JavierGONL/bd-pi/imagenes/BDPi reducido.jpg

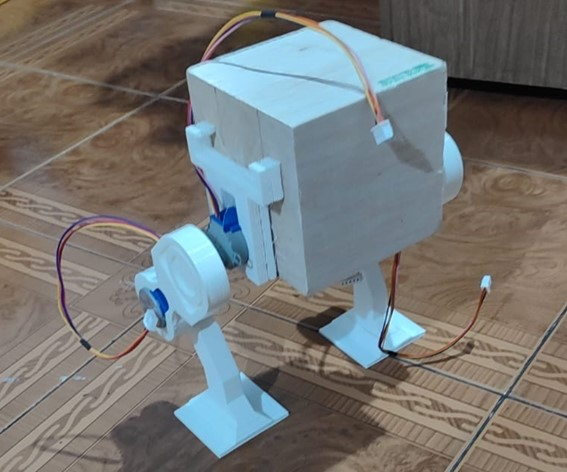
imagenes/BDPi reducido.jpg
