JavierGONL/bd-pi/imagenes/Black Box Actualizada.jpg

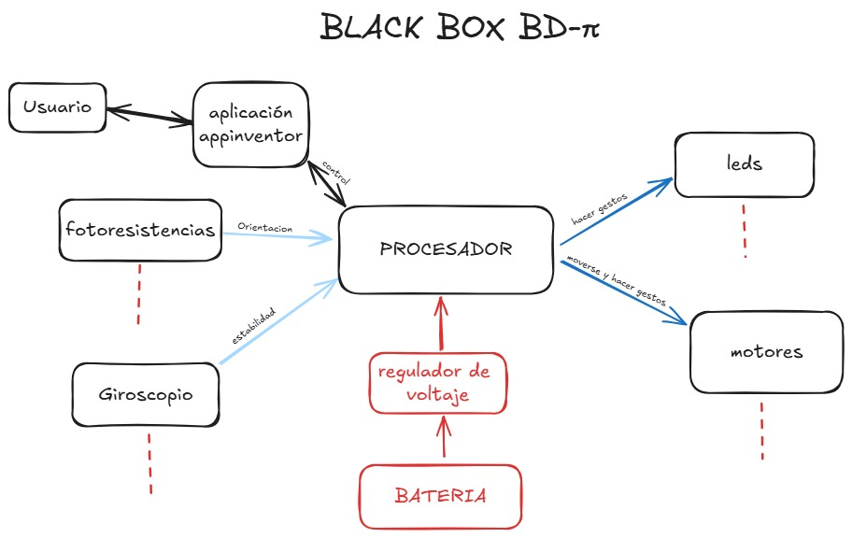
imagenes/Black Box Actualizada.jpg
