JavierGONL/bd-pi/imagenes/Caja Pico.jpg

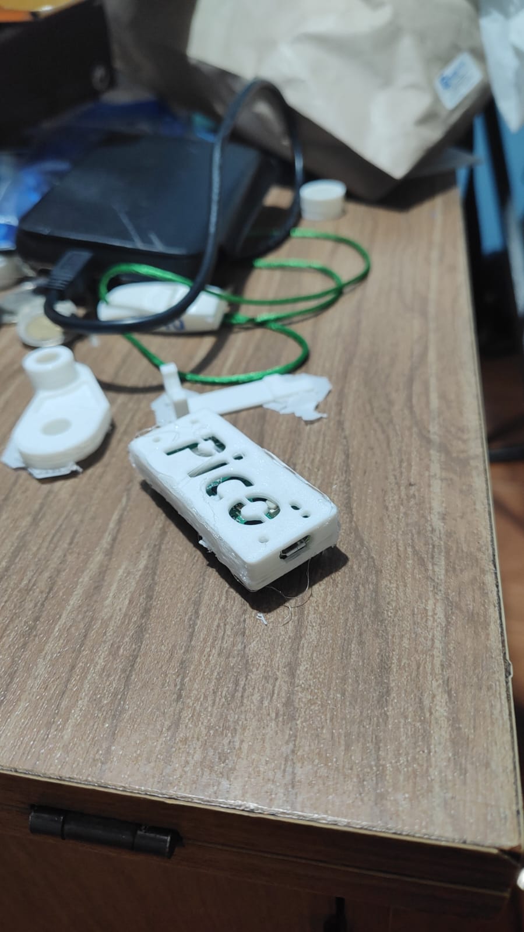
imagenes/Caja Pico.jpg
