JavierGONL/bd-pi/imagenes/Codigo App inventor.jpg

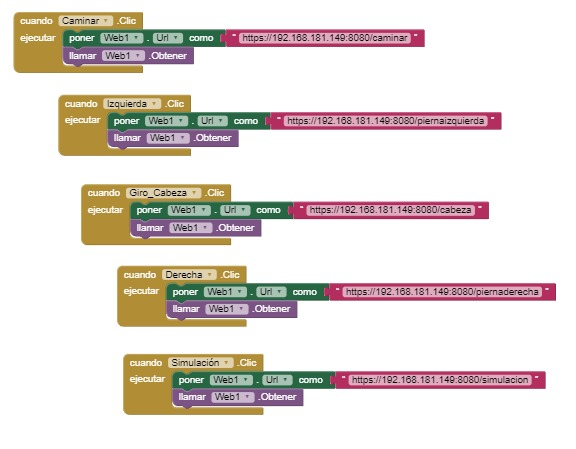
imagenes/Codigo App inventor.jpg
