JavierGONL/bd-pi/imagenes/esquematico.png

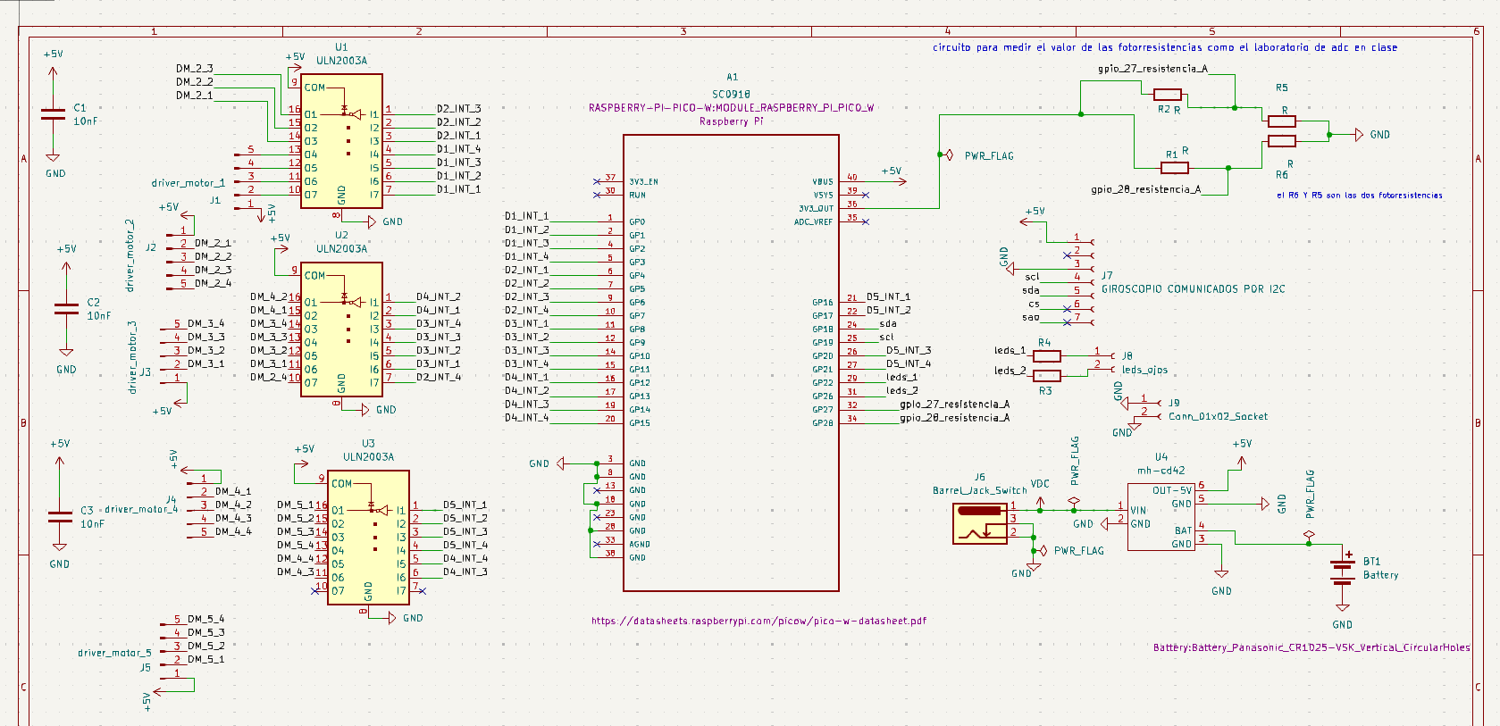
imagenes/esquematico.png
