JavierGONL/bd-pi/imagenes/Gray Box Actualizada.jpg

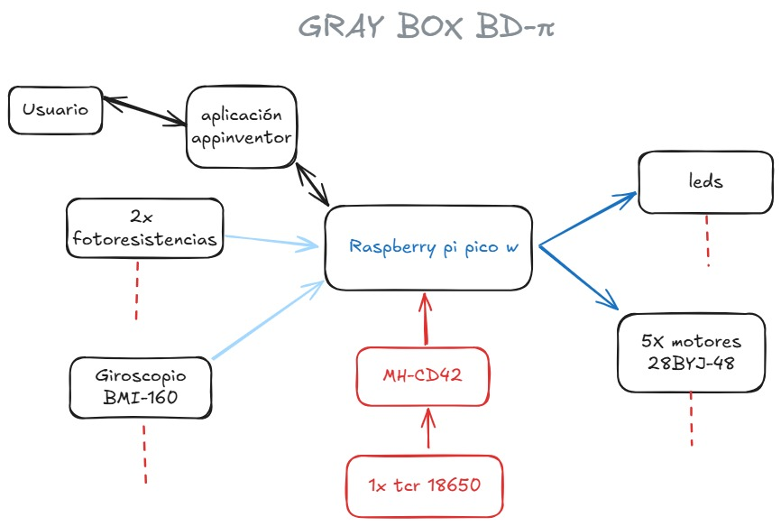
imagenes/Gray Box Actualizada.jpg
