JavierGONL/bd-pi/imagenes/Idea de Piernas.png

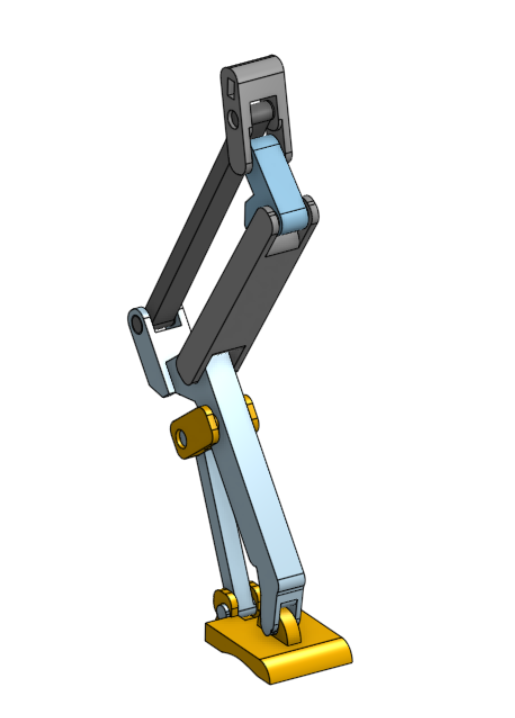
imagenes/Idea de Piernas.png
