JavierGONL/bd-pi/imagenes/Idea Final Pata Motores.jpg

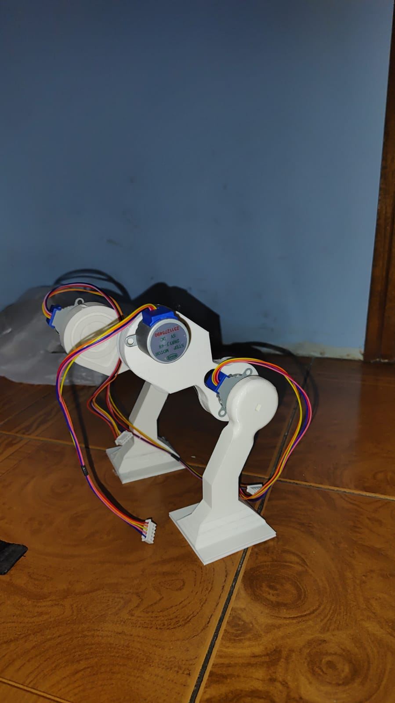
imagenes/Idea Final Pata Motores.jpg
