JavierGONL/bd-pi/imagenes/Imagen de Carga.jpg

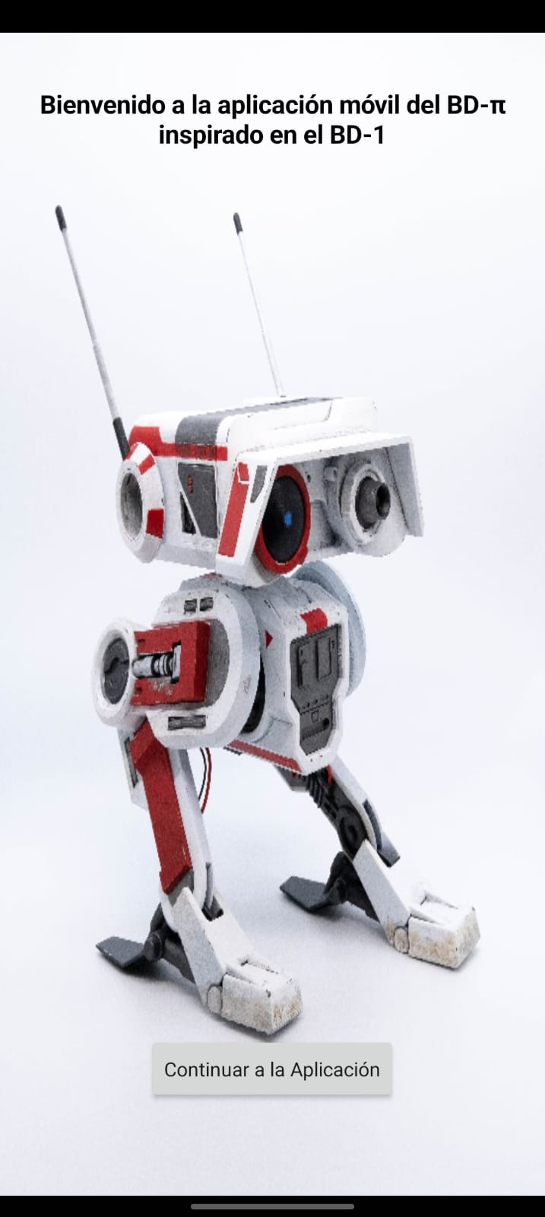
imagenes/Imagen de Carga.jpg
