JavierGONL/bd-pi/imagenes/Imagen Funcionalididad.jpg

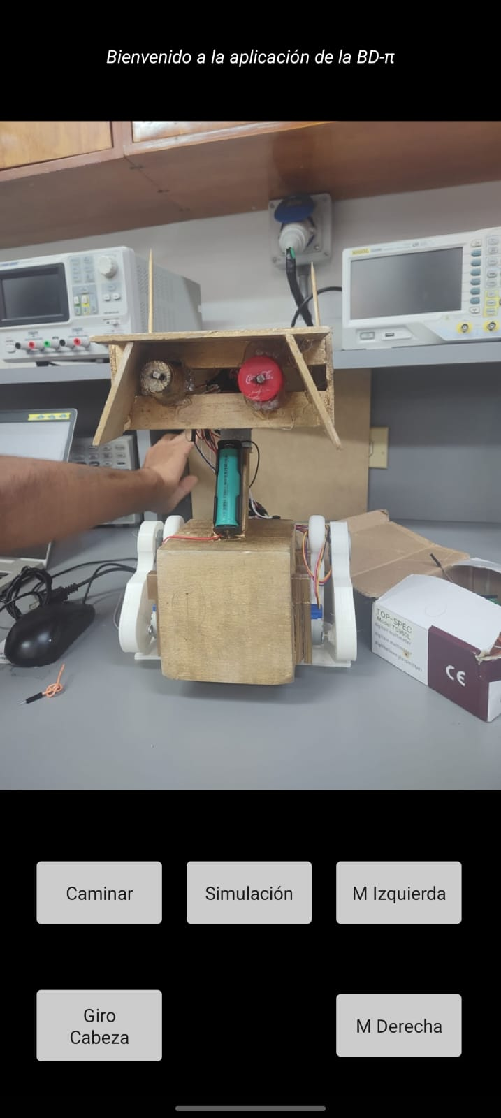
imagenes/Imagen Funcionalididad.jpg
