JavierGONL/bd-pi/imagenes/Imagen PCB.jpg

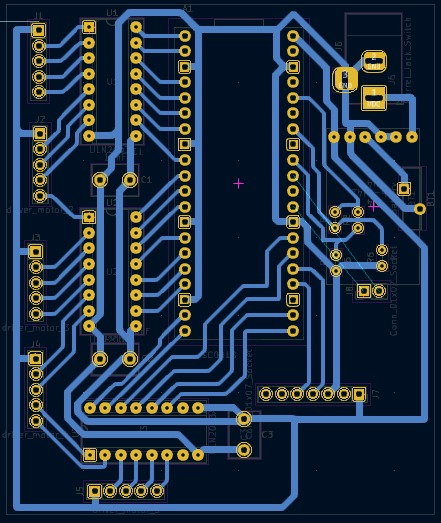
imagenes/Imagen PCB.jpg
