JavierGONL/bd-pi/imagenes/IMG_20240908_172200059.jpg

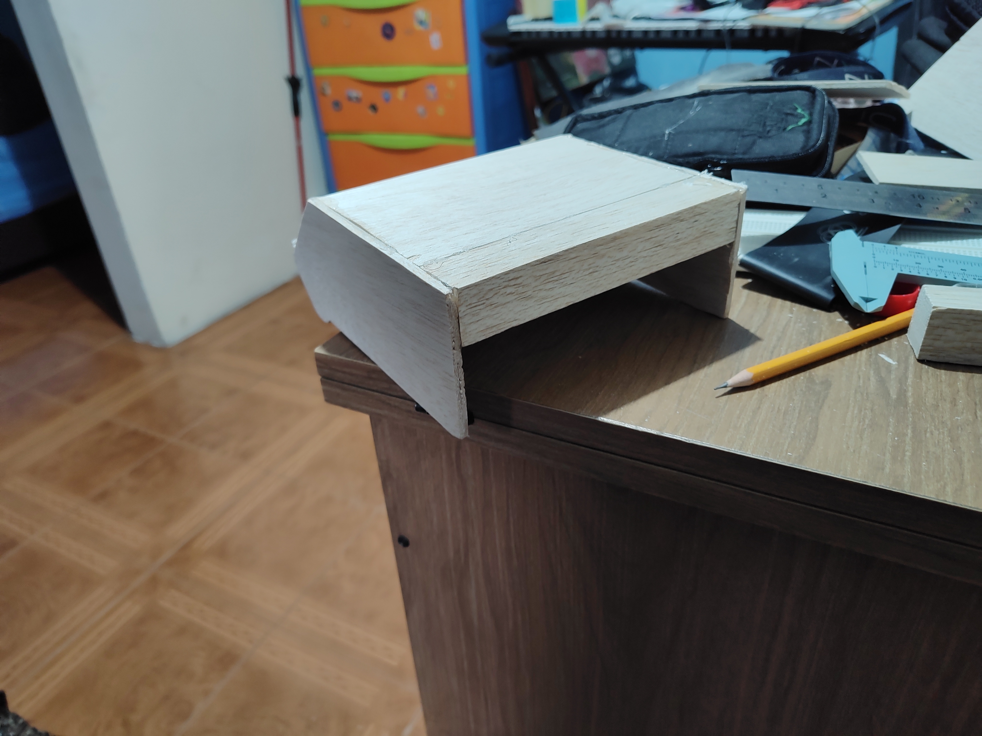
imagenes/IMG_20240908_172200059.jpg
