JavierGONL/bd-pi/imagenes/IMG_20240909_112415441.jpg

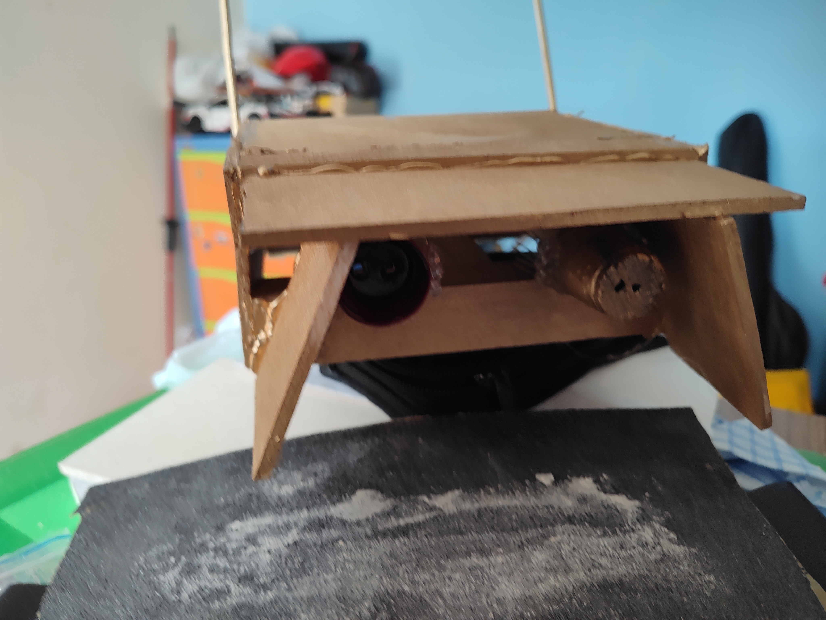
imagenes/IMG_20240909_112415441.jpg
