JavierGONL/bd-pi/imagenes/IMG_20240916_122246359.jpg

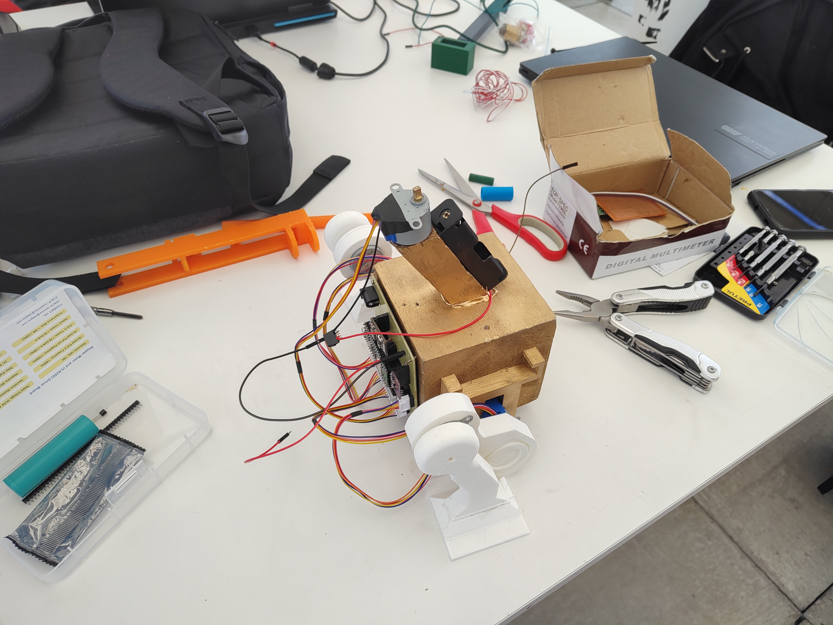
imagenes/IMG_20240916_122246359.jpg
