JavierGONL/bd-pi/imagenes/IMG_20240919_124108.jpg

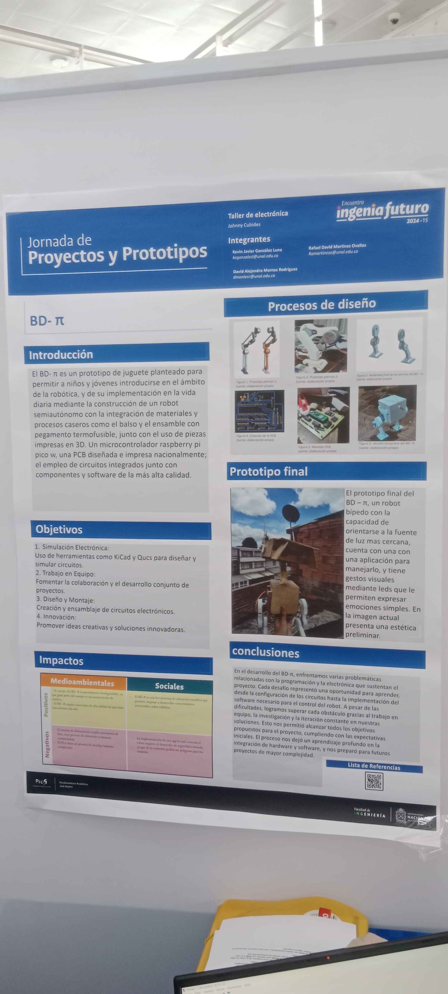
imagenes/IMG_20240919_124108.jpg
