JavierGONL/bd-pi/imagenes/IMG_20240919_124112.jpg

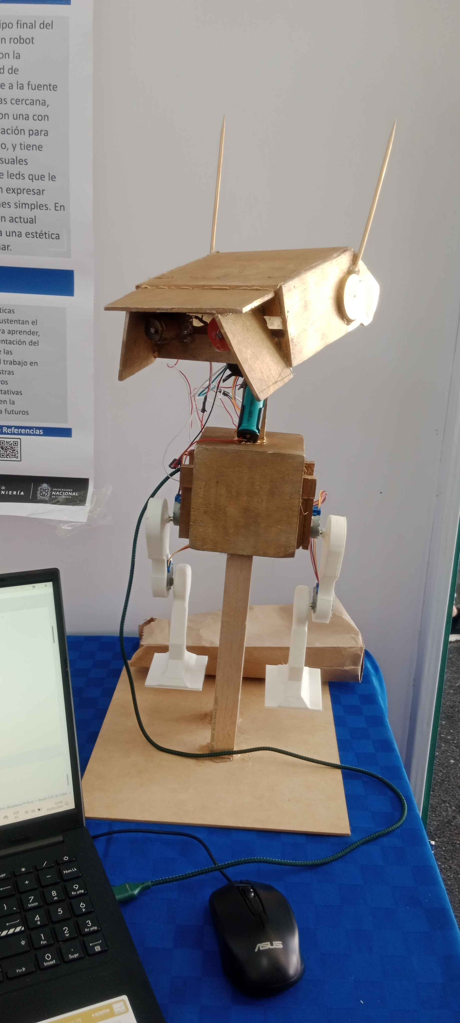
imagenes/IMG_20240919_124112.jpg
