JavierGONL/bd-pi/imagenes/IMG_20240919_124115.jpg

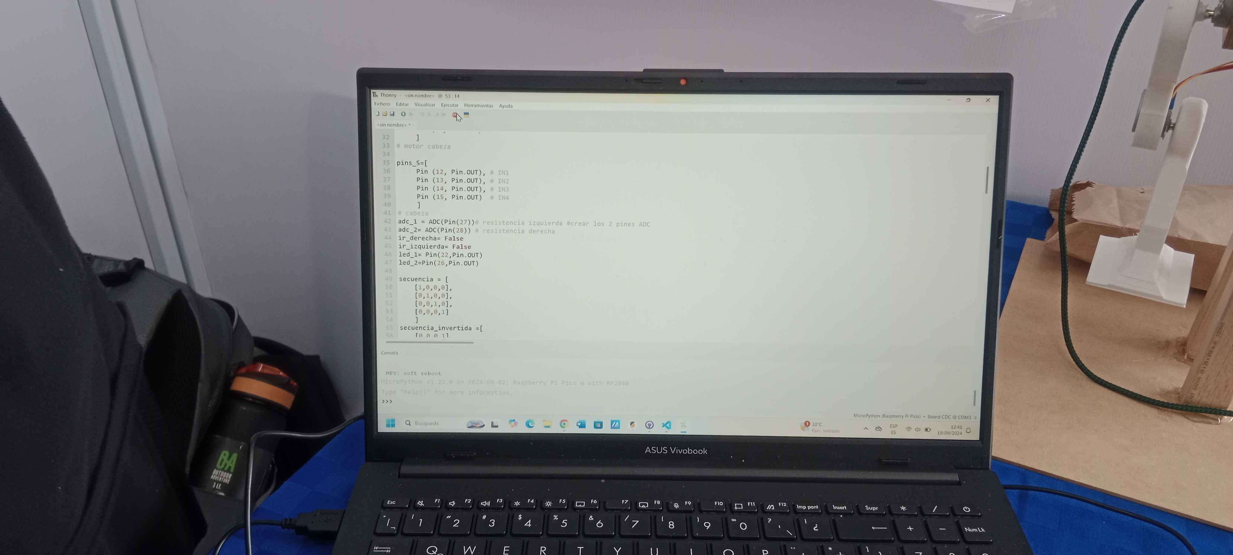
imagenes/IMG_20240919_124115.jpg
