JavierGONL/bd-pi/imagenes/IMG_20240919_124416.jpg

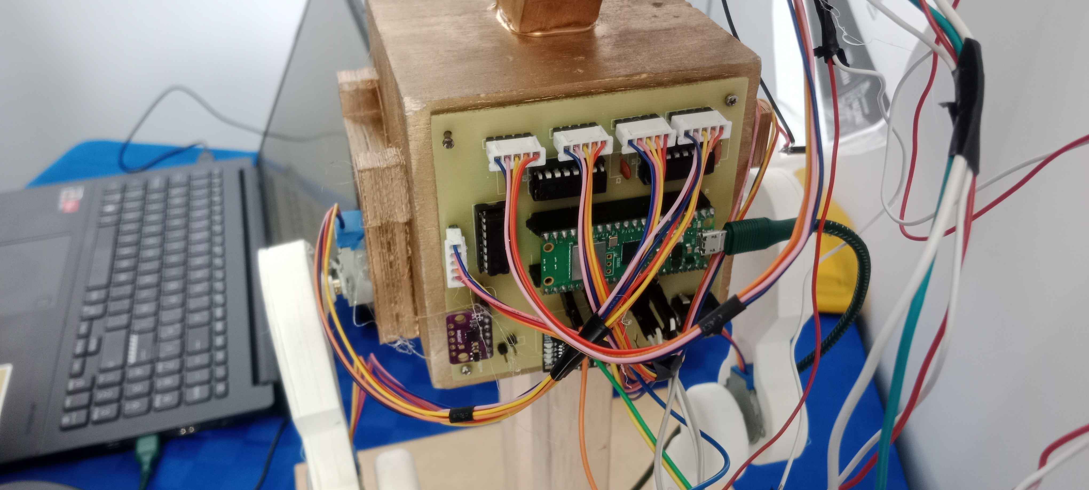
imagenes/IMG_20240919_124416.jpg
