JavierGONL/bd-pi/imagenes/IMG_20240923_212911483.jpg

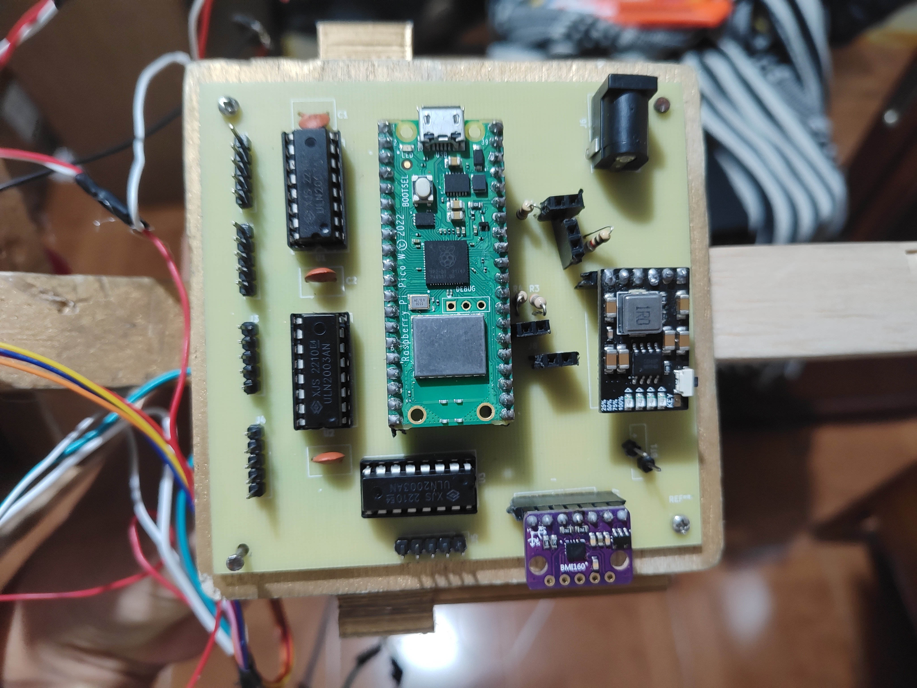
imagenes/IMG_20240923_212911483.jpg
