JavierGONL/bd-pi/imagenes/IMG_20240923_223421591.jpg

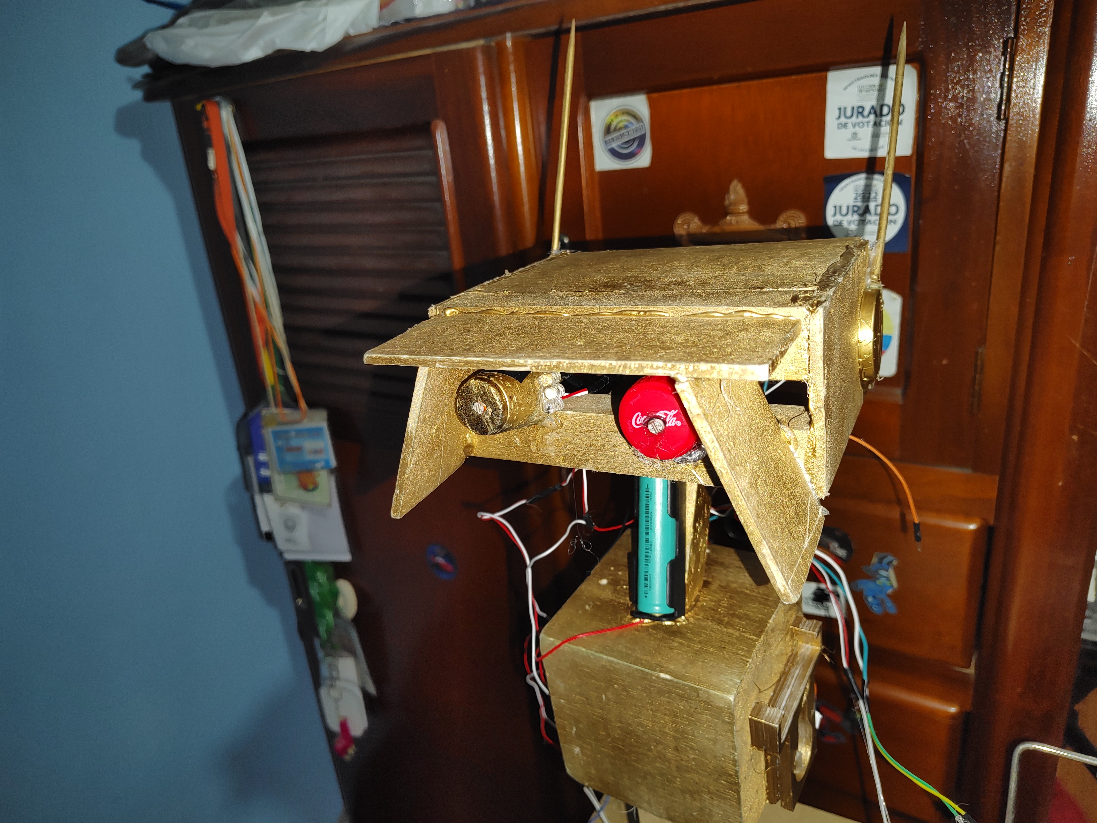
imagenes/IMG_20240923_223421591.jpg
