JavierGONL/bd-pi/imagenes/IMG_20240924_221900272.jpg

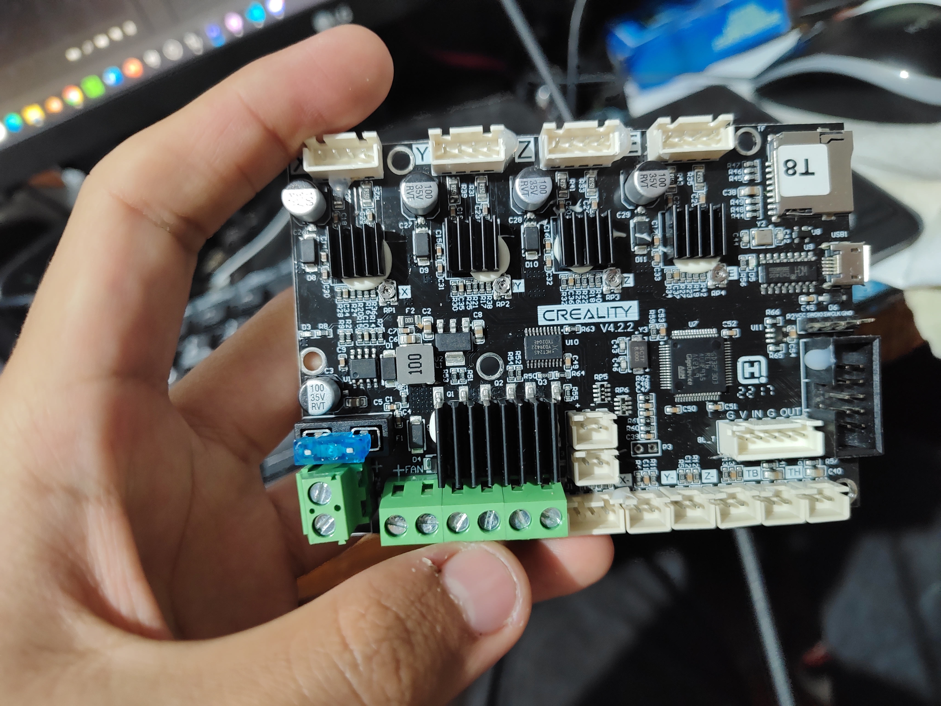
imagenes/IMG_20240924_221900272.jpg
