JavierGONL/bd-pi/imagenes/IMG_20240925_010636080.jpg

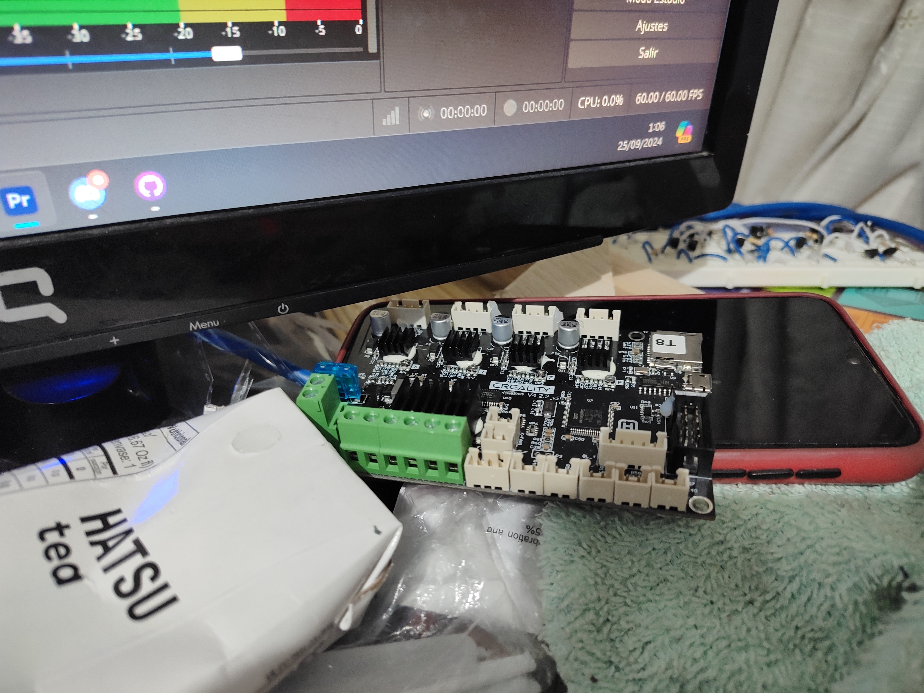
imagenes/IMG_20240925_010636080.jpg
