JavierGONL/bd-pi/imagenes/Impresión de patas.jpg

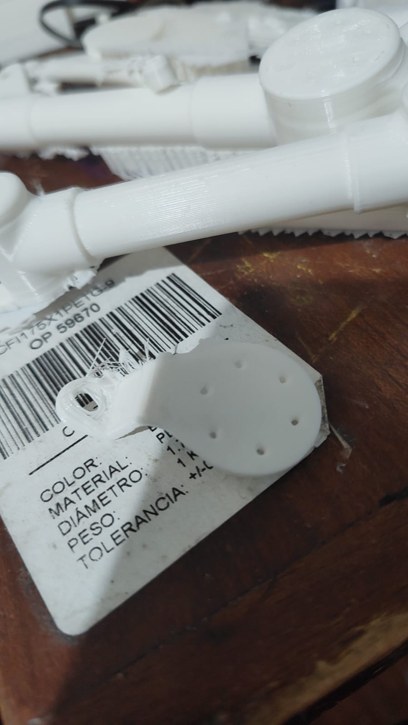
imagenes/Impresión de patas.jpg
