JavierGONL/bd-pi/imagenes/Mecanismo de Pata.jpg

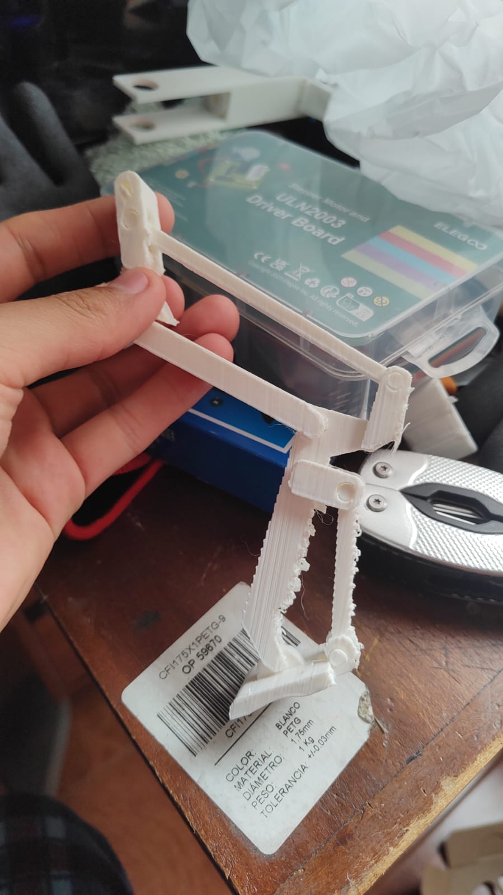
imagenes/Mecanismo de Pata.jpg
