JavierGONL/bd-pi/imagenes/Motores.jpg

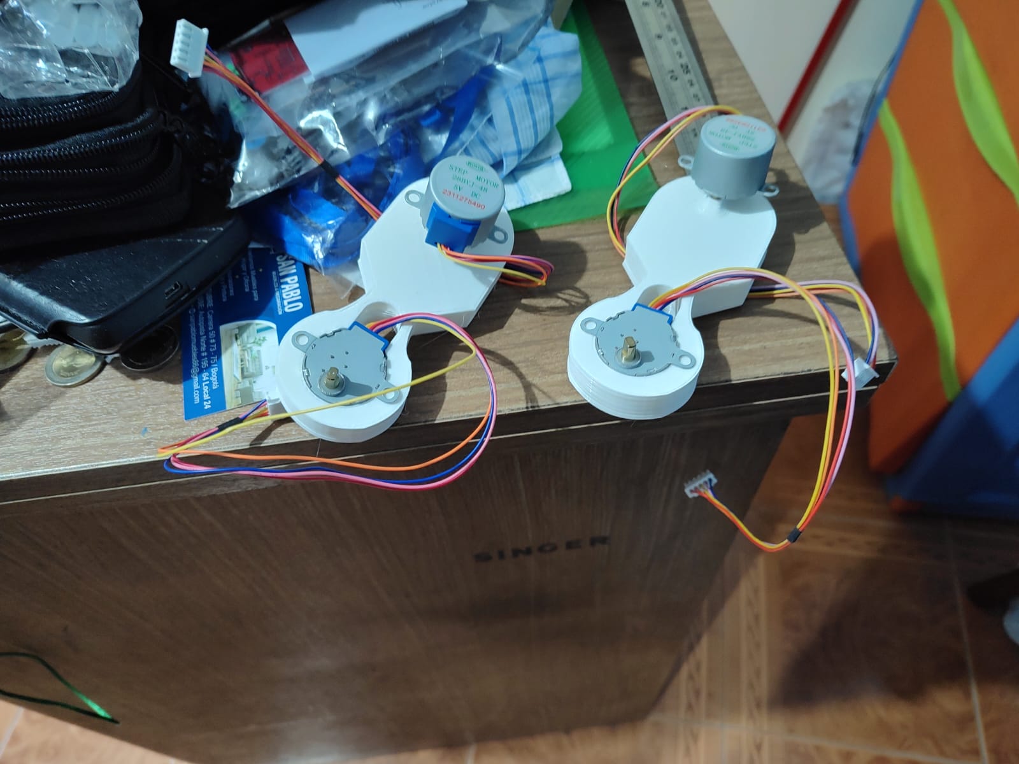
imagenes/Motores.jpg
