JavierGONL/bd-pi/imagenes/Pata Dañada.jpg

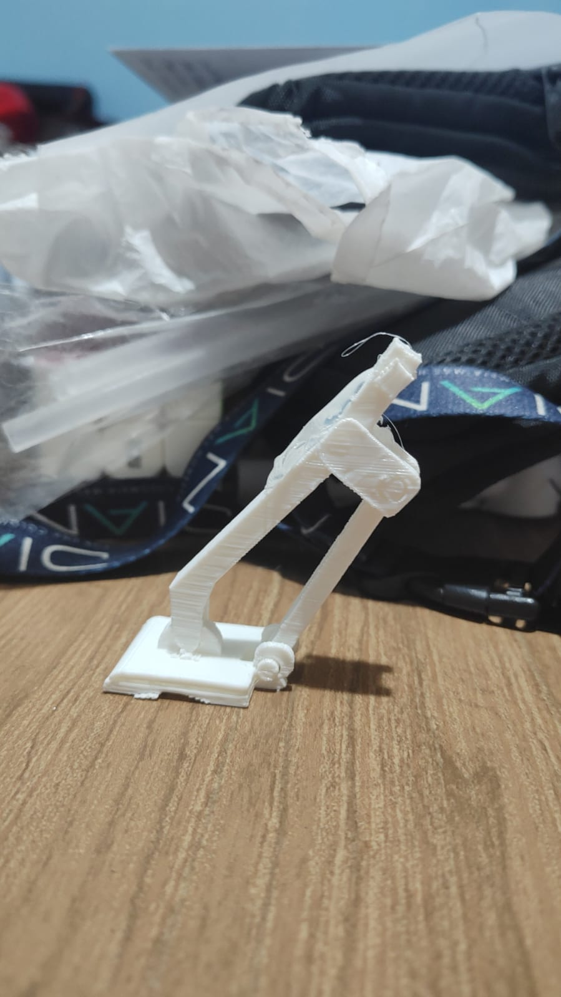
imagenes/Pata Dañada.jpg
