JavierGONL/bd-pi/imagenes/Patas Modeladas V2.png

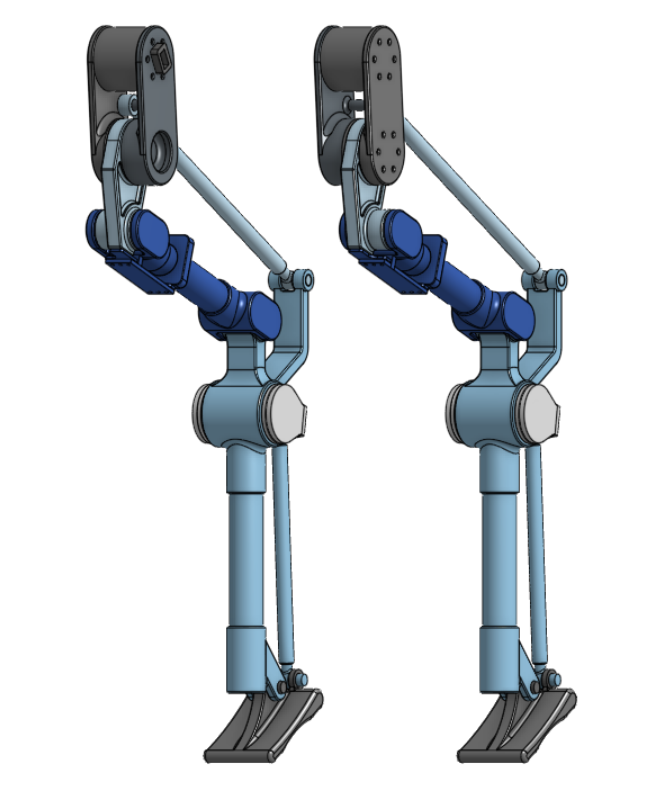
imagenes/Patas Modeladas V2.png
