JavierGONL/bd-pi/imagenes/Patas Modeladas V Final.png

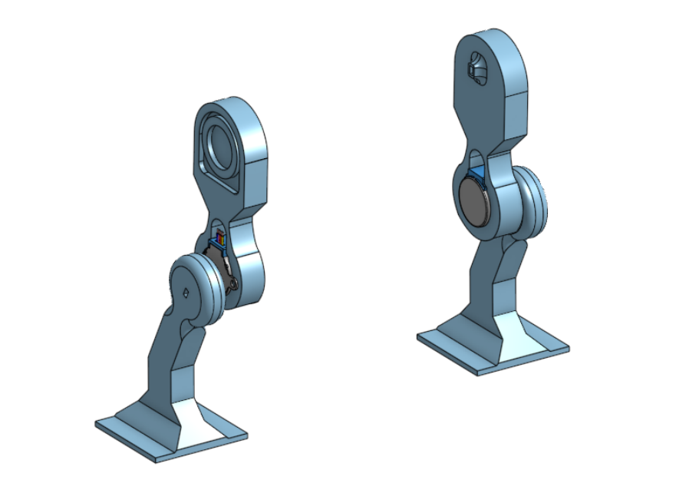
imagenes/Patas Modeladas V Final.png
