JavierGONL/bd-pi/imagenes/pcb desnuda.jpg

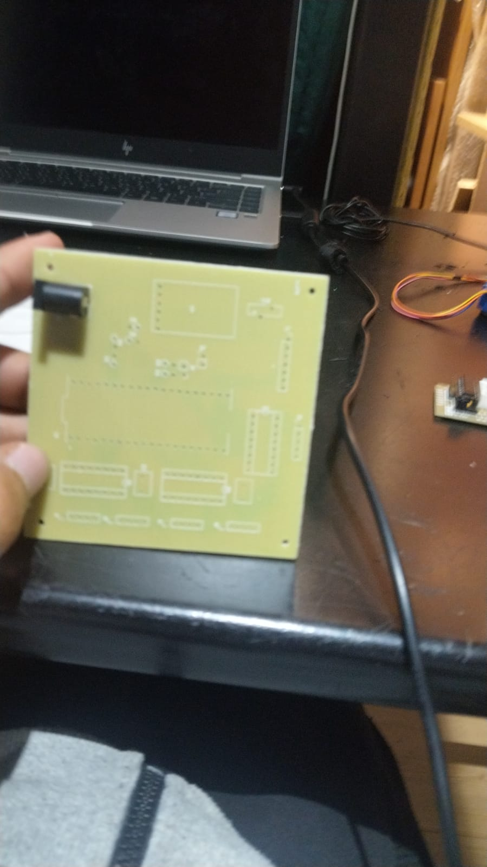
imagenes/pcb desnuda.jpg
