JavierGONL/bd-pi/imagenes/pcb.png

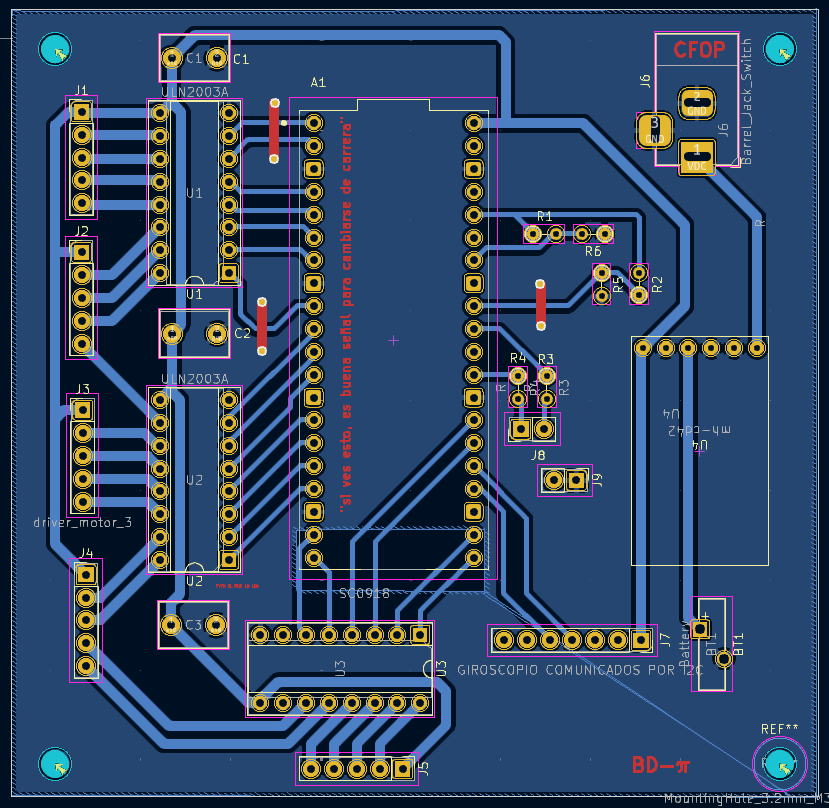
imagenes/pcb.png
