JavierGONL/bd-pi/imagenes/planteamiento original pcb.jpg

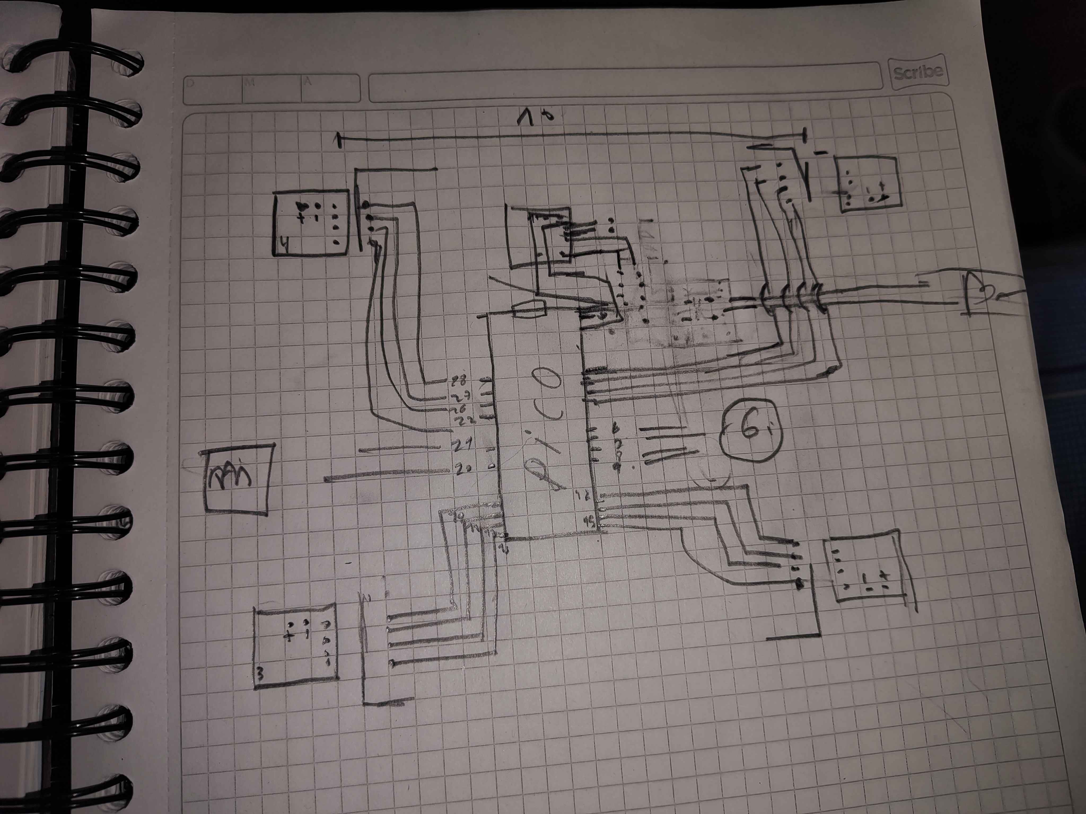
imagenes/planteamiento original pcb.jpg
