JavierGONL/bd-pi/imagenes/Screenshot_20240924-232021.png

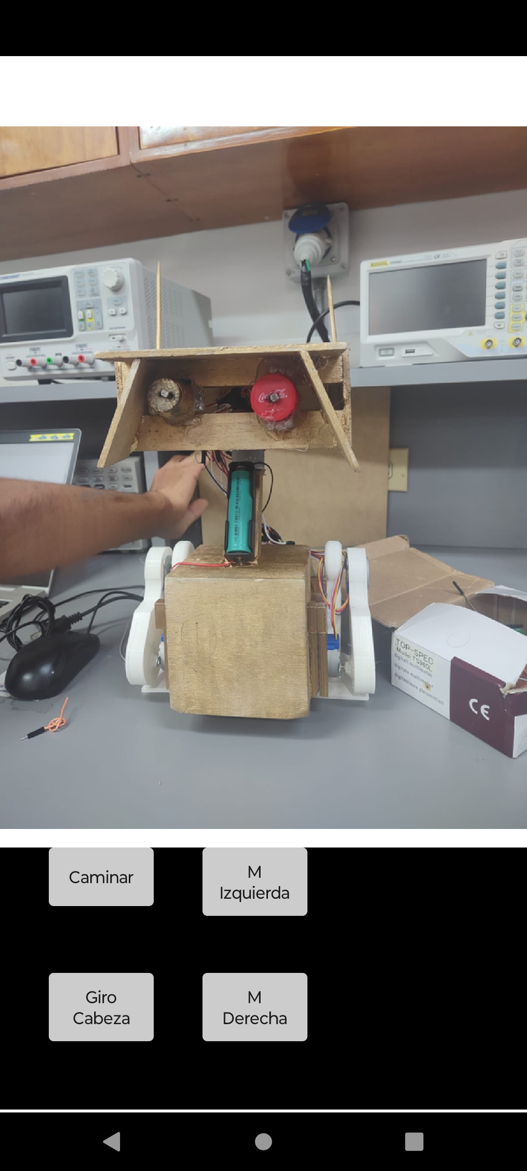
imagenes/Screenshot_20240924-232021.png
