JavierGONL/bd-pi/PCB/pcb_bd_pi.png

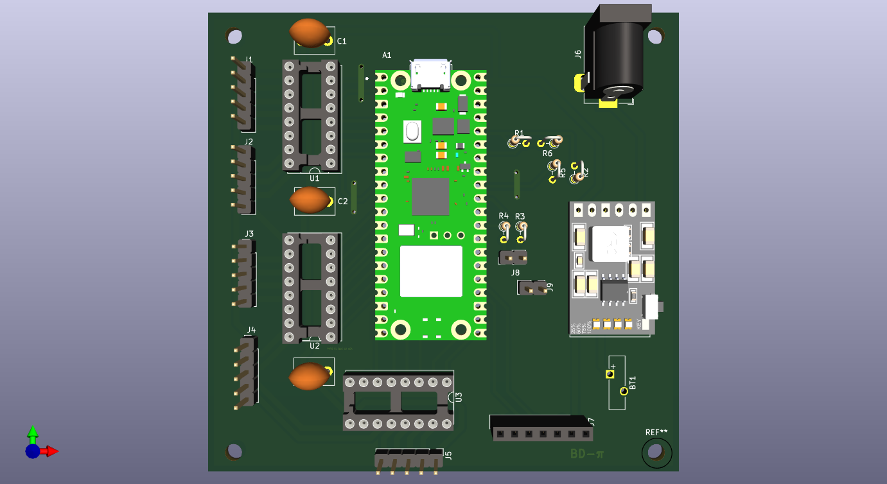
PCB/pcb_bd_pi.png
