JavierGONL/bd-pi/imagenes/BDPI armado.jpg

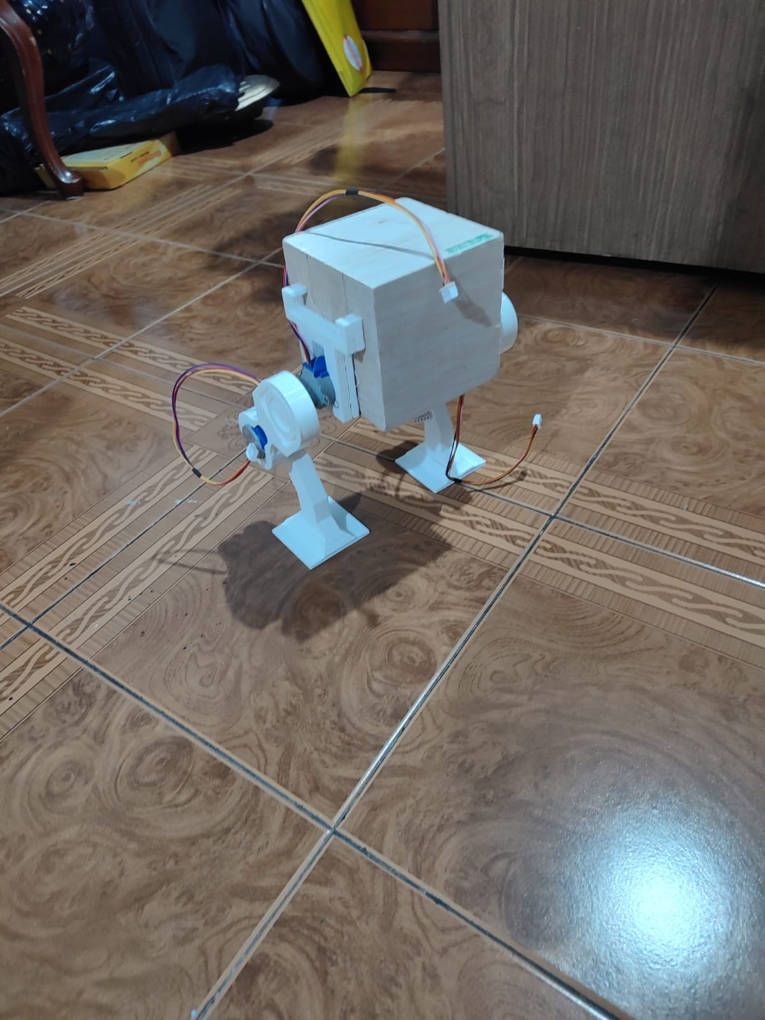
imagenes/BDPI armado.jpg
