JavierGONL/bd-pi/imagenes/Ensamble Sin Adornos.png

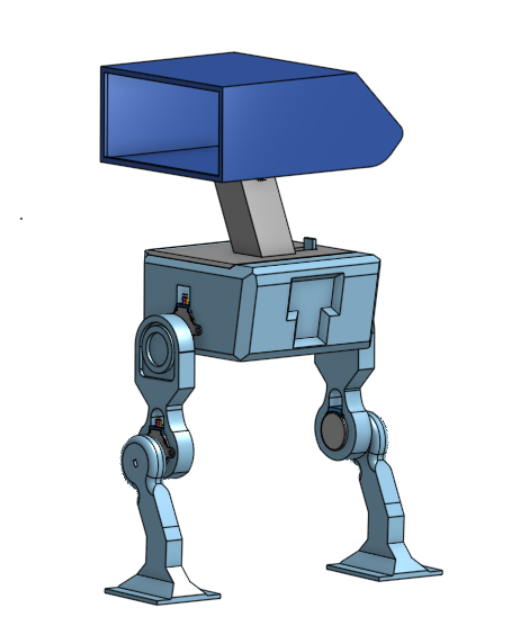
imagenes/Ensamble Sin Adornos.png
