JavierGONL/bd-pi/pruebas programacion/decodificador de bits copilot.py

# Cadena de bytes proporcionada
byte_string = b'\x16\x03\x01\x06\xe0\x01\x00\x06\xdc\x03\x03\xc8qw5\x1c9\x1ds\xc2\x86\x07\xa2`M\x1f\x96\xa8\x1bs\xed\x1f\x96\x16\x1ea\xbb\xfdR\xc4\xb1&r \xd4\xa4\xed\x91N7\xfe\xcb\xc9\xa9<\x11s%\x00*\xe7\xcc\xf6h\xfaM\xe8s\xfaM\x17\x06\xba6\xf8\xff\x00 \xba\xba\x13\x01\x13\x02\x13\x03\xc0+\xc0/\xc0,\xc00\xcc\xa9\xcc\xa8\xc0\x13\xc0\x14\x00\x9c\x00\x9d\x00/\x005\x01\x00\x06s**\x00\x00\x003\x04\xef\x04\xed\x1a\x1a\x00\x01\x00c\x99\x04\xc0\xbe\x07\x88\x8c\x08\xdf\xd17\x85\xd0\x04p\x01i\xd9\x85\xfcV9n"\x96\x9fl\xa3)\x816\xe5,\xe8\x1ah\xd9\x0f\xcau\xc5\xd4\xc2\xa74L\xa7l\x84\xa3V\x94S0l\xaeE\xc9\'\x0e[v\xf9i\xa8\xe5"6D\xe03\n\x01/\xe8"\x81\x89\xdc[\xd2H\x92\xfe\xa3\xbe\xedC\x87X\xec\x83uG\x1f\t3\x85\x1d\x97=\xe1t\x85\xd7\xc4\xcdb\xf9\x8a\xe2\xd5N\x0c\xf3\xb8\x12\xaaq\xe4s\x9ckr\x02\xabR\x1b\xf1\\@\t\xf4\x03\x07\x89A\x8e\xd3\x0cy\xc0\xb1X&\x84_\x9b\x90\xca\xa9h\xc6\x11;\x13\x80\xc5\x83\'\x80\xa1\xac\x1cr\xdaR\x109+\xe6\x02\x1f/a%TfZ\x08d\x85dTU ,\xbak\x89Z\xd0\xf2j\x1dz\x0e\xd9x\x00T\xf2\xb7\xcd\x03iM\x16gw\x86\xa9\x81\x93@\x0ftT\xb5\xb0-sv\x0b\xf4`\xacm\xd3.\x16\xdb\x1c\x9a\x1b\xb3\tF3K\x06s2\xf3x8%2Y\xc48(\xac\xca\x88\xe5\x11\x95\x85\x1b\xf5\x90\xb4>)\x81\xc2I\x1b\xea7~\xee\x970\xf1\x14RUz\xbc\x8b\xb7VC\x0bS\xf5\x93\x87x2\x82Y\xca\x83)\xebz\xdd\x18\xb2\x83D\xbd\xc1\xb0w\xc4a\x00\xe7\xe5\xba\x15\x14\x9f&\xd9\xbc\xd3\x92&\x11\xfa\\t<%\xb5\x88M\xc5A!x\xf2(\xfe\xe3H\xe5ep\xbd*pK\x80\n7ygU\xe5\x96\xf4\xeaN\xbb#\xb35CS\xaaJg\xec\x87`,\xda\x93\x12\x90{PU#\x86\xb1Ml\x00G\x87d\x1e\xdc\x00vg)ZR\xf4Y\xce\x12\x86\x94\x88\x94h\\.\xcd\x08QA\x94|\xb6\x067\xae\xa2dFt=\x0e\x90jy#\x03\xd9\xc2Z\x1ew\xbd\x17)P\xa5a\xa0crO\xe17rl\xa8\x05 \xf3\xb2T\xf7\x90\x80*x\x96\xa9%\xdf\x8c7\x06\'\xb3\xcd\xeb\xc5\xa3\xf9\xa9\xa7GBz\xb7\x97\xbbjDa\xbcC\xa2\xf2+\xec\x90\xa1\x8fC\x84\x1aI\xbc\xdf\xe4]\xd6<Ej\xd7k4\x89S&\x05\x80)6\xc9\xb6\x17R\xa0\x89\xaf\xe4\x9a]\xc4\x822\x13`\xb7\x83|x\x96\xe5\x02\x0e\xa0\xb8I\xa0\x9b\x06\xa9i\xe2\xf5`\x00\xc8\x03\xcb\x166\xee\x8b\xa8\x10\xa4\x80\x19L\xabRu\x9a4\'@e)\xb0F\xbb\xb2\x17\xec\x84\xdd\xd0\xa7\x8a\xbc\x91\xb5\xd8\x10H\x0b\xc7!\x80\x9a\x97 \x17j\x8at!vc\xe2\xd0:!{jJ\xd1y\x8e!\x06\x9fjJT\xb6Z\x96\x93\x84\x80\x9a\x8c\x0c\xc0L\r\xa5P\xa1\xb7\xac\x8e\xa4-vR\x08|3\x93`R\x16\xab\x06;\x8bR\xaf1Xz\xc5\xe9^\x009f1\x00x\xaf\xb1\xbd\xb9\xb2'

# Intentar decodificar la cadena de bytes a una cadena de texto
try:
    decoded_string = byte_string.decode('utf-8')
    print(decoded_string)
except UnicodeDecodeError as e:
    print(f"Error al decodificar: {e}")
