JavierGONL/bd-pi/imagenes/IMG_20240904_094058893.jpg

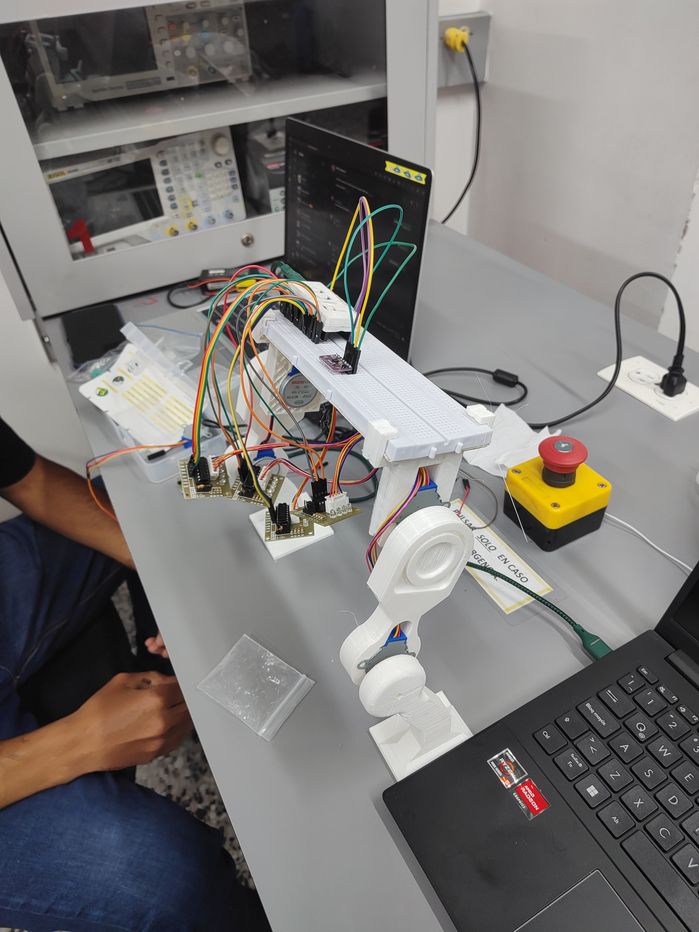
imagenes/IMG_20240904_094058893.jpg
